cdrfiuba/arion/Placa/placa.kicad_pcb

## KiCad design hardware/rumble.sch

Schematic: rumble.sch

Parts:
C1: 10uF
D1: 1N58XX
M: DC Motor
Q1: 2N7000; TO-92_Inline
R1: 1K
R2: 100K
